russellmcc/basspre-mm2/basspre.asc

C1: cap; 1µF
C2: cap; 1800pF
C3: cap; 47nF
C4: cap; 120pF
C5: cap; 500pF
C6: cap; 1µF
C7: cap; 10µF
R1: res; 220K
R2: res; 100K
R3: res; 500K
R4: res; 10K
R5: res; 500K
R6: res; 10K
R7: res; 100K
U1: opamp
V1: voltage; SINE(0 1v 10000); AC 1v
Named nets: 0
.ac oct 24 20 20000
.lib opamp.sub
